TuDo-Makerspace/MarioQuestionBlockCashBox/include/sounds.h

/*
 * sounds.h
 *
 * Author       : Yunis, Patrick Pedersen
 * Description  : Cointains sounds for the coin box
 * 
 */

#pragma once

#include <Arduino.h>

const unsigned char coin[] PROGMEM = {
  126, 127, 128, 128, 129, 129, 128, 127, 126, 127, 127, 127, 128, 128, 128, 128, 128, 127, 127, 127, 127, 128, 127, 128, 128, 128, 128, 
  128, 127, 126, 126, 126, 127, 128, 129, 129, 128, 127, 127, 126, 126, 127, 129, 129, 128, 129, 128, 126, 126, 127, 128, 127, 129, 130, 
  128, 127, 127, 126, 127, 128, 128, 129, 129, 127, 128, 126, 125, 127, 127, 126, 127, 128, 128, 128, 128, 127, 128, 126, 125, 125, 125, 
  126, 128, 128, 130, 129, 127, 126, 126, 126, 128, 129, 129, 130, 128, 126, 125, 124, 125, 127, 129, 128, 129, 129, 126, 127, 127, 128, 
  129, 128, 129, 129, 129, 128, 127, 128, 128, 128, 129, 128, 129, 130, 129, 129, 128, 128, 128, 130, 130, 129, 129, 128, 127, 127, 127, 
  129, 130, 131, 131, 129, 127, 123, 123, 125, 126, 129, 130, 129, 128, 125, 125, 127, 129, 129, 130, 128, 125, 126, 126, 127, 129, 130, 
  131, 128, 128, 126, 125, 128, 127, 129, 129, 128, 126, 126, 128, 126, 129, 128, 129, 130, 125, 131, 122, 129, 127, 132, 228, 255, 235, 
  241, 138, 96, 118, 101, 198, 245, 218, 233, 139, 81, 102, 84, 168, 233, 210, 225, 150, 71, 93, 76, 140, 227, 204, 219, 165, 67, 87, 67,
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
  }; 


const unsigned char powerup[] PROGMEM = {
  126, 126, 127, 127, 128, 129, 128, 128, 127, 127, 126, 127, 128, 128, 128, 128, 127, 127, 127, 126, 128, 128, 128, 128, 127, 126, 127, 127, 128, 127, 128, 128, 128, 128, 128, 129, 128, 127, 128, 126, 127, 127, 128, 130, 128, 129, 128, 126, 127, 126, 127, 129, 128, 129, 127, 125, 127, 127, 129, 130, 128, 128, 126, 125, 126, 126, 127, 128, 128, 129, 128, 128, 128, 128, 128, 127, 126, 126, 126, 127, 128, 128, 129, 128, 126, 127, 127, 128, 129, 126, 127, 127, 125, 128, 127, 129, 131, 129, 129, 126, 125, 127, 125, 128, 128, 128, 129, 128, 129, 128, 129, 129, 128, 127, 125, 126, 128, 127, 129, 128, 126, 127, 124, 124, 128, 127, 128, 129, 126, 126, 125, 126, 129, 129, 132, 130, 130, 129, 125, 126, 126, 126, 129, 126, 127, 125, 123, 126, 126, 129, 130, 129, 130, 127, 128, 130, 129, 131, 129, 126, 126, 123, 125, 126, 126, 129, 127, 130, 131, 128, 132, 129, 129, 131, 128, 129, 126, 126, 126, 126, 129, 127, 129, 128, 126, 129, 125, 127, 127, 127, 130, 126, 130, 127, 127, 130, 127, 130, 126, 127, 125, 124, 125, 123, 129, 124, 132, 126, 125, 215, 250, 239, 229, 132, 103, 121, 104, 115, 106, 113, 113, 112, 123, 102, 176, 241, 224, 229, 150, 88, 111, 99, 104, 103, 102, 108, 102, 117, 97, 137, 226, 223, 228, 181, 92, 102, 101, 96, 103, 93, 103, 93, 107, 103, 110, 208, 228, 222, 206, 101, 87, 102, 90, 107, 97, 106, 101, 99, 106, 88, 170, 227, 217, 222, 135, 83, 103, 89, 98, 94, 96, 103, 96, 112, 92, 141, 225, 216, 223, 167, 83, 98, 93, 94, 101, 93, 105, 94, 108, 98, 109, 206, 221, 218, 195,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
};

const unsigned char oneup[] PROGMEM = {
  126, 126, 128, 129, 128, 127, 126, 126, 128, 129, 129, 126, 125, 126, 127, 129, 130, 128, 127, 126, 128, 130, 131, 129, 126, 125, 126, 129, 130, 129, 126, 126, 127, 129, 130, 129, 126, 125, 126, 127, 128, 126, 127, 127, 126, 128, 128, 126, 126, 125, 126, 127, 127, 128, 126, 126, 127, 127, 127, 127, 127, 127, 127, 128, 129, 129, 128, 127, 127, 128, 128, 129, 129, 128, 127, 127, 127, 130, 130, 129, 128, 127, 129, 129, 129, 126, 125, 128, 129, 130, 129, 129, 129, 129, 129, 128, 128, 128, 127, 128, 129, 130, 129, 128, 128, 128, 127, 127, 129, 129, 128, 128, 126, 127, 127, 127, 127, 126, 127, 127, 128, 128, 128, 128, 127, 126, 126, 127, 128, 129, 129, 127, 128, 129, 128, 130, 128, 128, 126, 127, 128, 128, 128, 126, 127, 128, 128, 131, 128, 129, 125, 125, 130, 126, 134, 124, 130, 200, 247, 224, 159, 103, 118, 181, 232, 220, 151, 96, 103, 168, 223, 213, 149, 89, 94, 156, 214, 211, 147, 86, 82, 144, 206, 209, 150, 82, 79, 131, 204, 236, 168, 81, 69, 132, 216, 233, 167, 82, 59, 121, 205, 229, 170, 83, 54, 109, 196, 228, 173, 86, 49, 99, 187, 226, 178, 90, 47, 91, 179, 223, 182, 94, 45, 84, 172, 223, 186, 98, 44, 77, 163, 218, 190, 104, 45, 71, 155, 217, 195, 110, 45, 64, 147, 214, 200, 117, 47, 59, 139, 211, 203, 123, 51, 54, 131, 207, 207, 131, 53, 50, 124, 202, 209, 137, 57, 47, 116, 198, 212, 144, 61, 43, 109, 194, 214, 151, 65, 41, 101, 187, 216, 158, 72, 40, 94, 181, 216, 164, 76, 39, 86, 168, 207, 165, 82, 41, 81, 164, 208, 171, 89, 42, 76, 157, 207, 177, 97, 44, 71, 151, 206,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
};
